ChillGal/Custom-Macro-Keyboard/Photos/BaseMountRender.PNG

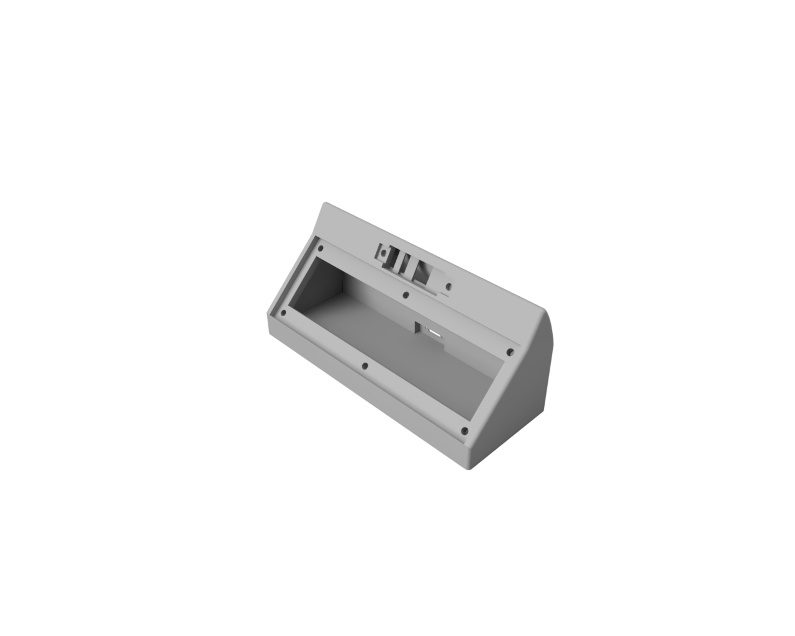
Photos/BaseMountRender.PNG
