ChillGal/Custom-Macro-Keyboard/Photos/KeyPlateRender.png

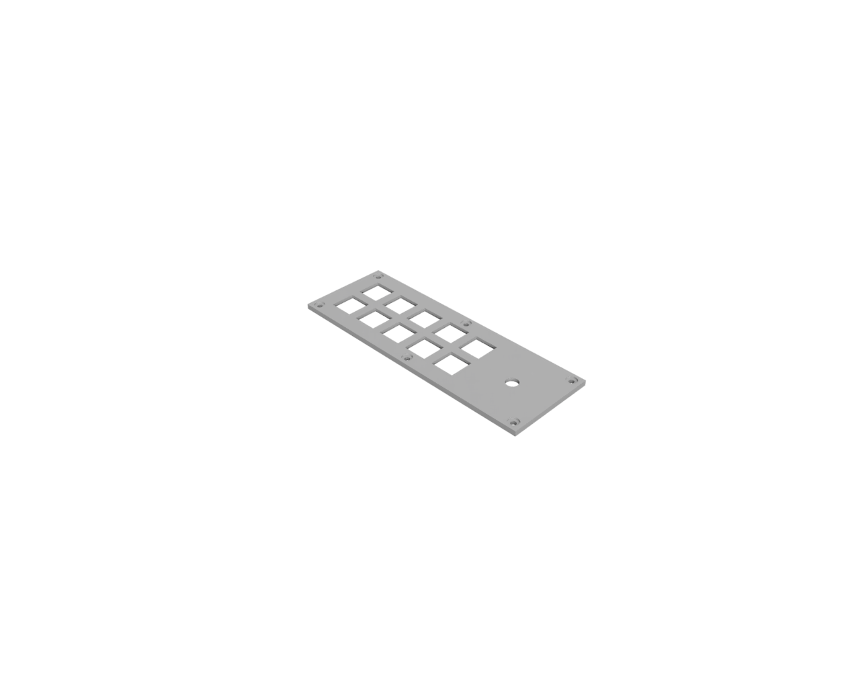
Photos/KeyPlateRender.png
